SedlJa/Passman/_docs/app_archi.png

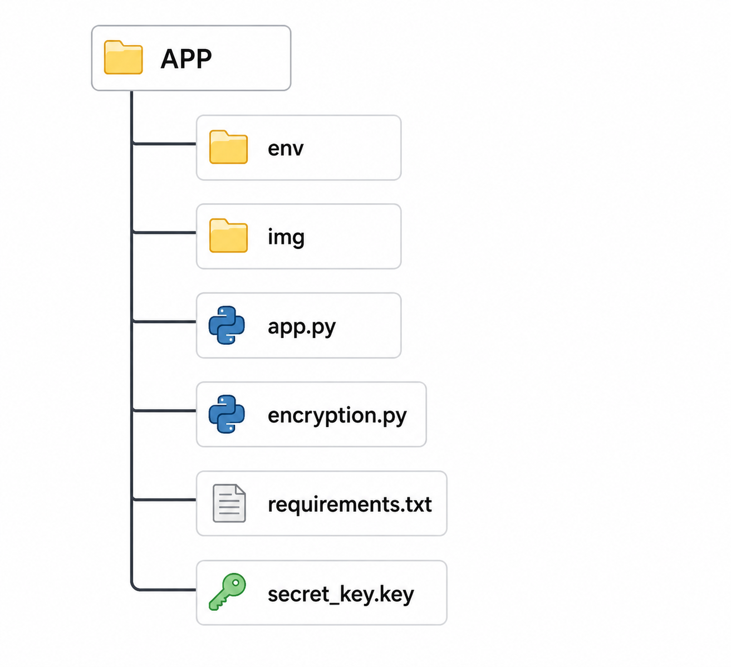
_docs/app_archi.png
