SedlJa/Passman/_docs/fw_diagram_bold.png

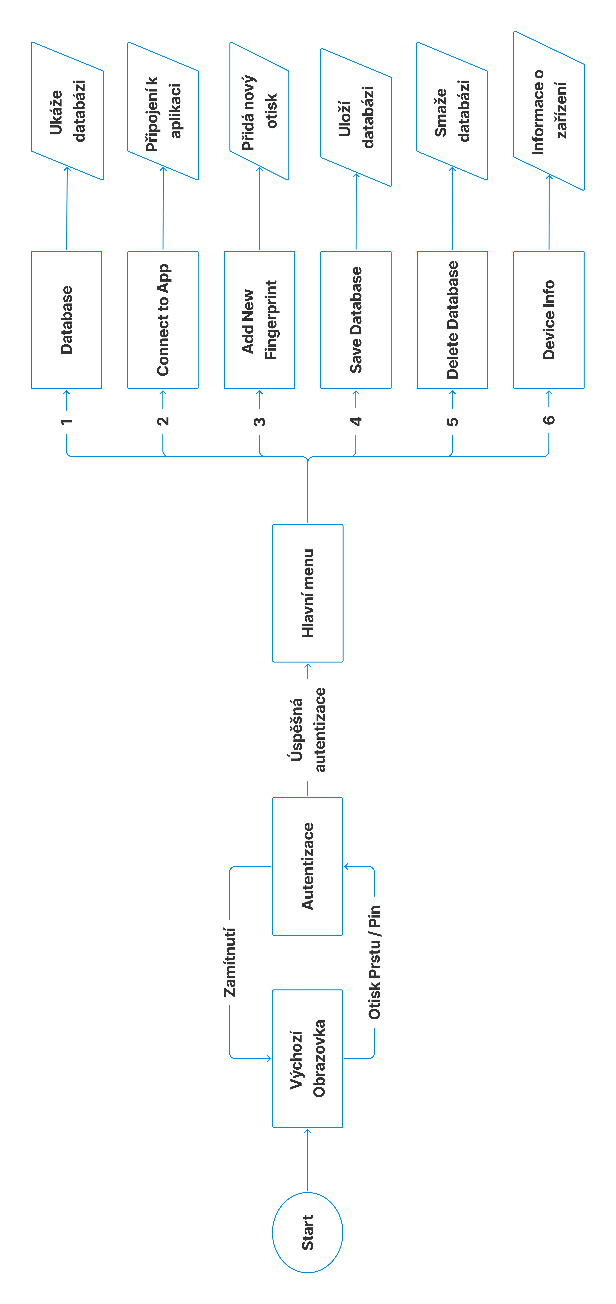
_docs/fw_diagram_bold.png
