SedlJa/Passman/_docs/layout_2v1.png

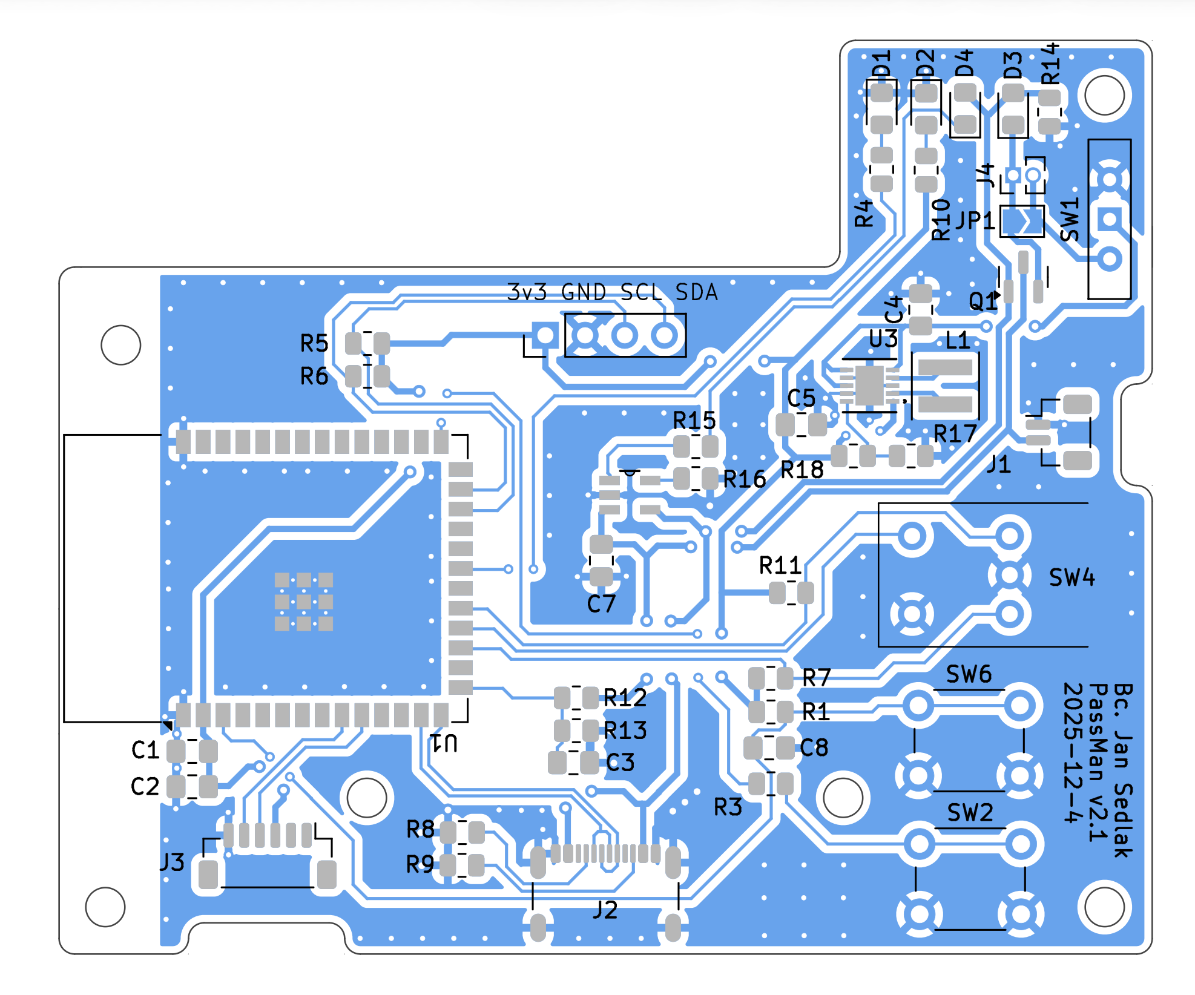
_docs/layout_2v1.png
