SedlJa/Passman/HW/Fusion/side2_view.png

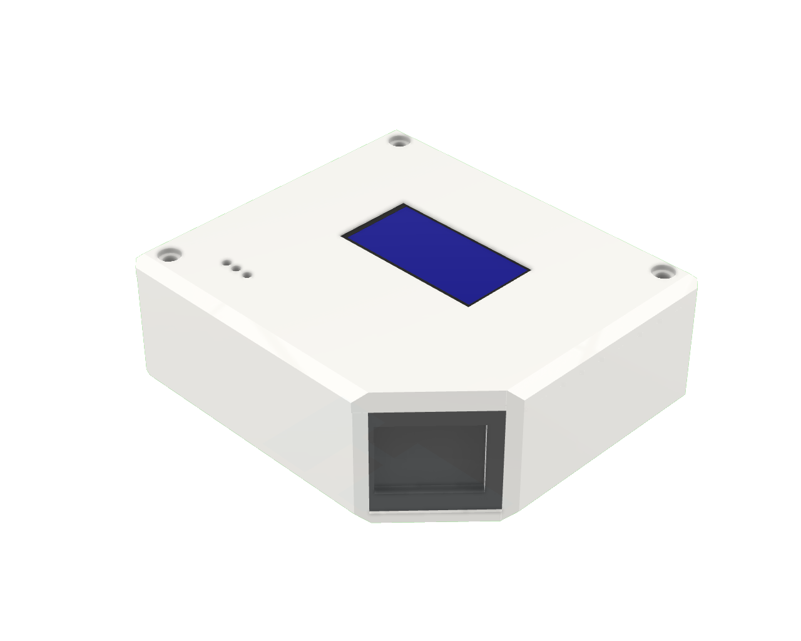
HW/Fusion/side2_view.png
