SedlJa/Passman/HW/Fusion/side_view2.png

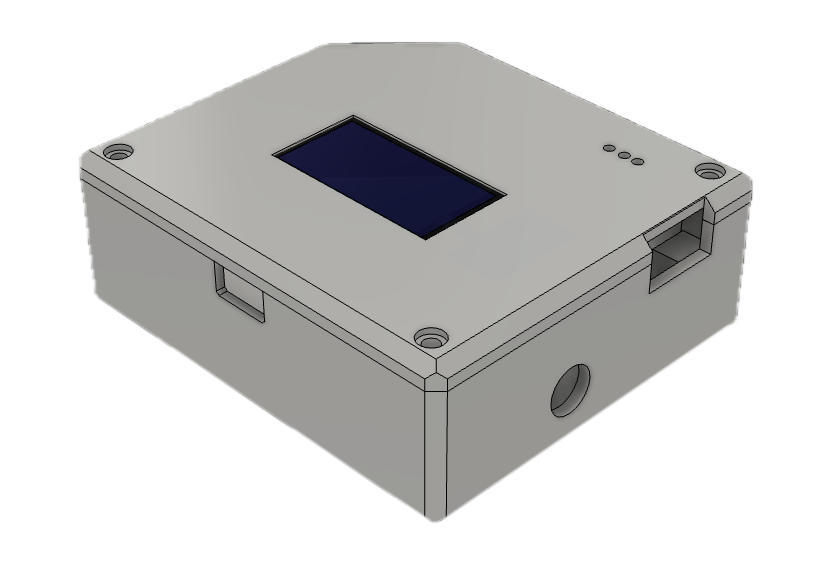
HW/Fusion/side_view2.png
