SedlJa/Passman/HW/Fusion/side_view.png

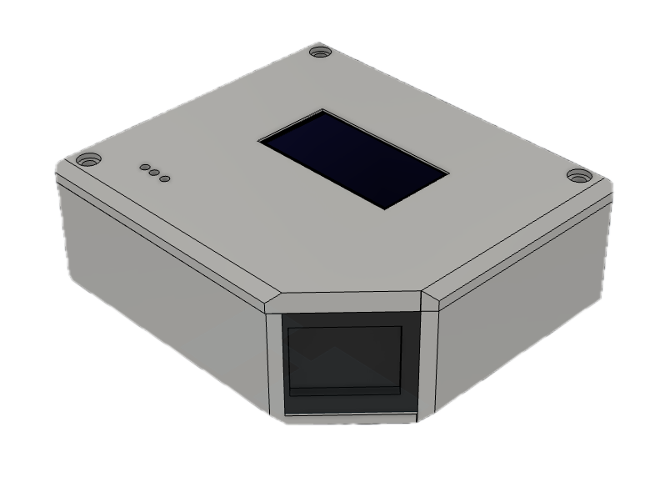
HW/Fusion/side_view.png
