SedlJa/Passman/HW/Fusion/sideview_device.png

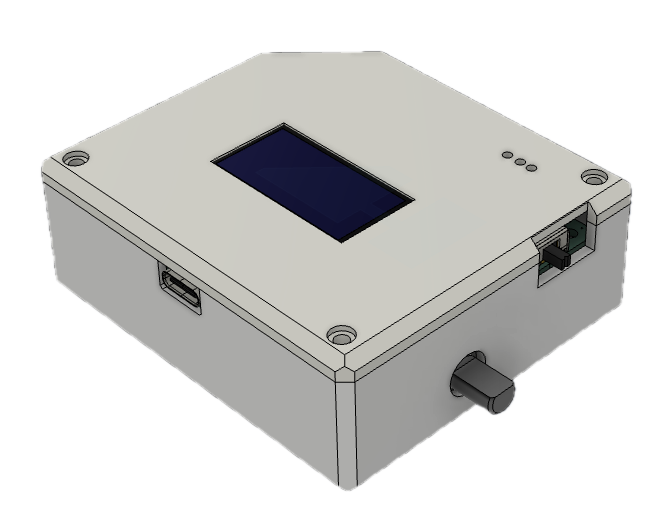
HW/Fusion/sideview_device.png
