SedlJa/Passman/HW/Fusion/top_view.png

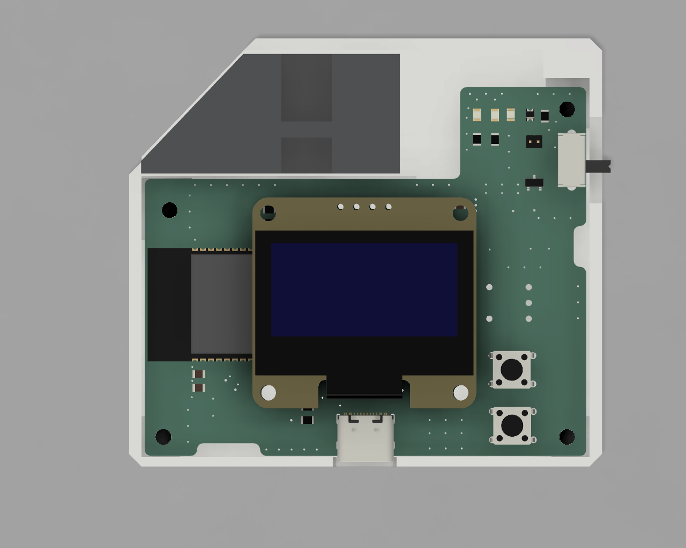
HW/Fusion/top_view.png
