SedlJa/Passman/HW/Fusion/top_view_box.png

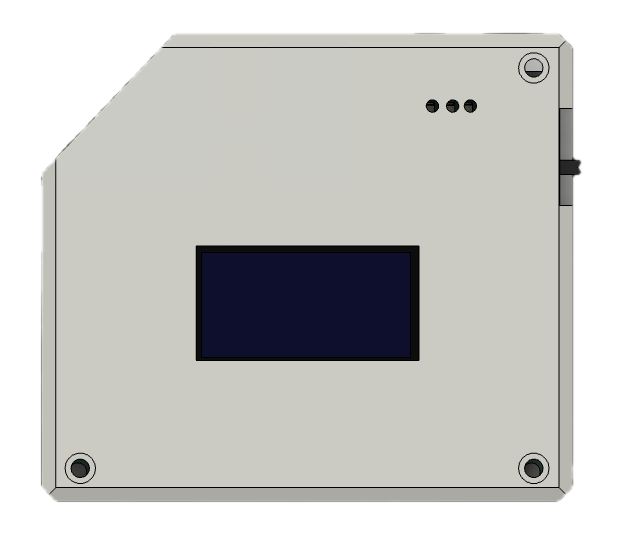
HW/Fusion/top_view_box.png
