SedlJa/Passman/HW/Fusion/top_view_device.png

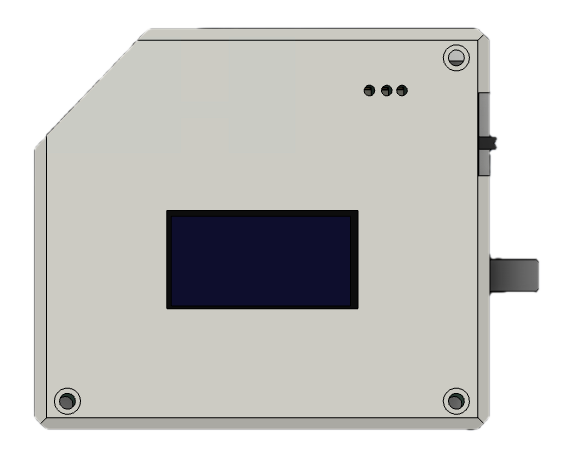
HW/Fusion/top_view_device.png
