SedlJa/Passman/HW/pcb_2v1.png

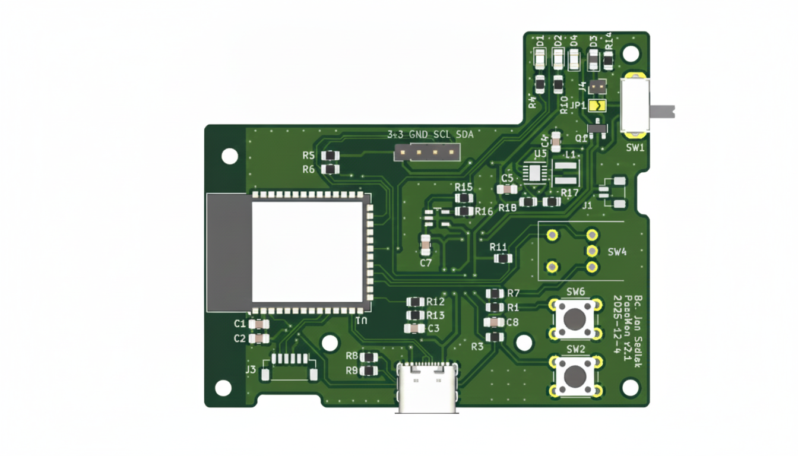
HW/pcb_2v1.png
