SedlJa/Passman/SW/firmware/src/oled.cpp

#include "oled.h"
#include "i2c_finder.h"
#include "database.h"

/* Defines */
#define DELAYTIME 1000
#define DISPLAYI2C_ADDR 0x3C
#define DISPLAYWIDTH 128
#define DISPLAYHEIGH 64
#define BATT_LVL 3 // battery level read pin

/* Create diplay instance */
Adafruit_SH1106G display = Adafruit_SH1106G(DISPLAYWIDTH, DISPLAYHEIGH, &Wire, -1);

/* Functions */

/* Battery lvl function */
int getBatteryLevelPercentage(int pin)
{
    int raw = analogRead(BATT_LVL);

    float v = (raw / 4095.0) * 3.3;

    // kompenzace děliče
    v *= 2.0;

    // Convert voltage to percentage
    float percentage = (v - 3.0) / (3.9 - 3.0) * 100.0; // Assuming 3.0V is 0% and 4.2V is 100%
    percentage = constrain(percentage, 0.0, 100.0);     // Clamp the value between 0% and 100%

    // Round percentage to the nearest multiple of 5
    percentage = round(percentage / 5.0) * 5.0;
    return percentage;
}

/**
 * @brief function that setups OLED display
 */
void display_setup()
{
    Wire.setPins(48, 47); // Set I2C pins [sda, scl ]
    Wire.begin();         // Inicializace I2C

    int state; // OLED I2C state
    state = find_I2C_addr();
    if (state == 0)
    {
        Serial.print("OLED display found.\r\n");
    }
    else if (state == 1)
    {
        Serial.println("No I2C device found.\r\n");
    }
    else if (state == 2)
    {
        Serial.println("Unknown error.\r\n");
    }

    display.begin(DISPLAYI2C_ADDR, true);
    display.clearDisplay();
    display.setTextColor(SH110X_WHITE);
    display.setTextSize(1);
}

void test_print(int rotaryVal)
{
    // put your main code here, to run repeatedly:
    display.setCursor(0, 7);
    display.println((String) "Teplota: 25C");
    display.println((String) "Tlak: 950hPa");
    display.println((String) "Vlhkost: 65%");
    display.println((String) "Loviskuju ZUZANKU");
    display.println((String) "Rotary value: " + (String)rotaryVal);
    display.display();
    delay(10);
    display.clearDisplay();
}

void getID(int rotaryVal)
{
    // put your main code here, to run repeatedly:
    display.setCursor(0, 20);
    display.println((String) "new ID: " + (String)rotaryVal);
    display.display();
    delay(10);
    display.clearDisplay();
}

/**
 * @brief function for displaying the fingerprint sensor while unlocking the device
 */
void unlockPage()
{
    // 1st stage
    display.clearDisplay();
    display.drawBitmap(0, 0, epd_bitmap_fpsensor, 128, 64, SH110X_WHITE);
    display.display();
    delay(20);
    display.clearDisplay();
}
/**
 * @brief Function that shows tick while authentication passed
 */
void unlockSuccessfull(int ledpin)
{
    // stage 1
    digitalWrite(ledpin, HIGH); // turn on LED
    display.clearDisplay();
    display.drawBitmap(0, 0, epd_bitmap_tick, 128, 64, SH110X_WHITE);
    display.display();
    delay(1000);
    display.clearDisplay();
    // stage 2
    display.drawBitmap(0, 0, epd_bitmap_tick2, 128, 64, SH110X_WHITE);
    display.display();
    delay(1000);
    display.clearDisplay();
    // stage 1
    display.drawBitmap(0, 0, epd_bitmap_tick3, 128, 64, SH110X_WHITE);
    display.display();
    delay(1000);
    display.clearDisplay();
    digitalWrite(ledpin, LOW); // Turn off led
}

/**
 * @brief function for displaying the first page
 */
void menuPage1()
{
    // put your main code here, to run repeatedly:
    display.clearDisplay();
    display.drawBitmap(0, 0, epd_bitmap_database, 128, 64, SH110X_WHITE);
    display.display();
    delay(10);
    display.clearDisplay();
}

/**
 * @brief function for displaying the second page
 */
void menuPage2()
{
    // put your main code here, to run repeatedly:
    display.clearDisplay();
    display.drawBitmap(0, 0, epd_bitmap_connect, 128, 64, SH110X_WHITE);
    display.display();
    delay(10);
    display.clearDisplay();
}

/* enroll FP */
void placeFP()
{
    display.clearDisplay();
    display.setCursor(30, 15);
    display.println("Place Finger");
    display.display();
    delay(10);
    display.clearDisplay();
}
void remove()
{
    display.clearDisplay();
    display.setCursor(30, 15);
    display.println("Remove Finger");
    display.display();
    delay(10);
    display.clearDisplay();
}
void addedFP()
{
    display.clearDisplay();
    display.setCursor(20, 15);
    display.println("Fingerprint added!");
    display.display();
    delay(10);
    display.clearDisplay();
}

void failFP()
{
    display.clearDisplay();
    display.setCursor(20, 15);
    display.println("No match found!");
    display.display();
    delay(10);
    display.clearDisplay();
}

/**
 * @brief function for displaying the fourth page
 */
void menuPage4()
{
    // put your main code here, to run repeatedly:
    display.clearDisplay();
    display.drawBitmap(0, 0, epd_bitmap_savedb, 128, 64, SH110X_WHITE);
    display.display();
    delay(10);
    display.clearDisplay();
}

/**
 * @brief function for displaying the fourth page
 */
void menuPage5()
{
    // put your main code here, to run repeatedly:
    display.clearDisplay();
    display.drawBitmap(0, 0, epd_bitmap_deleteall, 128, 64, SH110X_WHITE);
    display.display();
    delay(10);
    display.clearDisplay();
}

/**
 * @brief function for displaying the fourth page
 */
void menuPage6()
{
    // put your main code here, to run repeatedly:
    display.clearDisplay();
    display.drawBitmap(0, 0, epd_bitmap_devinfo, 128, 64, SH110X_WHITE);
    display.display();
    delay(10);
    display.clearDisplay();
}

void menuPage3()
{
    display.clearDisplay();
    display.drawBitmap(0, 0, epd_bitmap_addFP, 128, 64, SH110X_WHITE);
    display.display();
    delay(10);
    display.clearDisplay();
}

/**
 * @brief Function for choose upload/download page
 */
void uploadPage()
{
    display.clearDisplay();
    display.drawBitmap(0, 0, epd_bitmap_upload, 128, 64, SH110X_WHITE);
    display.display();
    delay(10);
    display.clearDisplay();
}
/**
 * @brief Function for choose upload/download page
 */
void downloadPage()
{
    display.clearDisplay();
    display.drawBitmap(0, 0, epd_bitmap_download, 128, 64, SH110X_WHITE);
    display.display();
    delay(10);
    display.clearDisplay();
}

/**
 * @brief Page that shows each database item
 */
void databasePage(int dbEntry)
{
    display.setCursor(0, 0);
    display.println((String)db.id[dbEntry]);
    display.println((String) "");
    display.println((String) "Username:");
    display.println((String)db.username[dbEntry]);
    display.println((String) " ");
    display.println((String) " ");
    display.println((String) "Password");
    display.println((String)db.password[dbEntry]);
    display.display();
    delay(10);
    display.clearDisplay();
}

/**
 * @brief function for displaying the author info Page
 */
void deviceInfo()
{
    // Open the JSON file
    FILE *file = fopen("/spiffs/device.json", "r");
    if (!file)
    {
        Serial.println("Failed to open deviceinfo.json");
        return;
    }

    // Read the file into a buffer
    char buffer[256];
    size_t bytesRead = fread(buffer, 1, sizeof(buffer) - 1, file);
    buffer[bytesRead] = '\0'; // Null-terminate the buffer
    fclose(file);

    // Parse the JSON data
    StaticJsonDocument<512> doc;
    DeserializationError error = deserializeJson(doc, buffer);
    if (error)
    {
        Serial.print("Failed to parse JSON: ");
        Serial.println(error.c_str());
        return;
    }

    // Extract data from JSON
    JsonObject deviceInfo = doc["deviceInfo"];
    const char *deviceName = deviceInfo["device Name"];
    const char *fwVersion = deviceInfo["FW Version"];
    const char *hwVersion = deviceInfo["HW Version"];
    const char *serialNumber = deviceInfo["SN"];

    // Display the data on the OLED
    display.clearDisplay();
    display.setCursor(0, 0);
    display.println("Device Info:");
    display.println((String) "");
    display.println((String) "Project: " + deviceName);
    display.println((String) "FW Ver:  " + fwVersion);
    display.println((String) "HW Ver:  " + hwVersion);
    display.println((String) "SN:      " + serialNumber);
    display.println((String) "Battery: " + getBatteryLevelPercentage(BATT_LVL) + " %");
    display.display();
}
// 'database', 128x64px
const unsigned char epd_bitmap_database[] PROGMEM = {
    0x00, 0x00, 0x00, 0x00, 0x00, 0x00, 0x00, 0x00, 0x00, 0x00, 0x00, 0x00, 0x00, 0x00, 0x00, 0x00,
    0x00, 0x00, 0x00, 0x00, 0x00, 0x00, 0x00, 0x00, 0x00, 0x00, 0x00, 0x00, 0x00, 0x00, 0x00, 0x00,
    0x00, 0x00, 0x00, 0x00, 0x00, 0x00, 0x00, 0x00, 0x00, 0x00, 0x00, 0x00, 0x00, 0x00, 0x00, 0x00,
    0x00, 0x00, 0x00, 0x00, 0x00, 0x00, 0x00, 0x00, 0x00, 0x00, 0x00, 0x00, 0x00, 0x00, 0x00, 0x00,
    0x00, 0x00, 0x00, 0x00, 0x00, 0x00, 0x00, 0x00, 0x00, 0x00, 0x00, 0x00, 0x00, 0x00, 0x00, 0x00,
    0x00, 0x00, 0x00, 0x00, 0x00, 0x00, 0x00, 0x00, 0x00, 0x00, 0x00, 0x00, 0x00, 0x00, 0x00, 0x00,
    0x00, 0x00, 0x00, 0x00, 0x00, 0x00, 0x00, 0x00, 0x00, 0x00, 0x00, 0x00, 0x00, 0x00, 0x00, 0x00,
    0x00, 0x00, 0x00, 0x00, 0x00, 0x00, 0x00, 0x00, 0x00, 0x00, 0x00, 0x00, 0x00, 0x00, 0x00, 0x00,
    0x00, 0x00, 0x00, 0x00, 0x00, 0x00, 0x00, 0x00, 0x00, 0x00, 0x00, 0x00, 0x00, 0x00, 0x00, 0x00,
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
    epd_bitmap_database,
    epd_bitmap_savedb,
    epd_bitmap_download,
    epd_bitmap_upload,
    epd_bitmap_devinfo,
    epd_bitmap_deleteall,
    epd_bitmap_fpsensor,
    epd_bitmap_tick,
    epd_bitmap_tick2,
    epd_bitmap_tick3,
    epd_bitmap_connect,
    epd_bitmap_addFP,
};
