SedlJa/Passman/SW/firmware/src/encryption.cpp

/* Includes */
#include "encryption.h"
#include "esp_efuse.h"

/* Defines */
static uint8_t secret_key[AES_KEY_SIZE];
static bool secret_key_loaded = false;

/* Functions */
static bool load_secret_key_from_efuse()
{
    if (secret_key_loaded)
    {
        return true;
    }

    esp_err_t err = esp_efuse_read_block(EFUSE_BLK_USER_DATA, secret_key, 0, AES_KEY_SIZE * 8);
    if (err != ESP_OK)
    {
        Serial.printf("Error: Failed to read AES key from eFuse. Code: %d\n", err);
        return false;
    }

    bool key_is_empty = true;
    for (size_t i = 0; i < AES_KEY_SIZE; i++)
    {
        if (secret_key[i] != 0)
        {
            key_is_empty = false;
            break;
        }
    }

    if (key_is_empty)
    {
        Serial.println("Error: AES key in eFuse is empty.");
        return false;
    }

    secret_key_loaded = true;
    return true;
}

void print_secret_key_debug()
{
    if (!load_secret_key_from_efuse())
    {
        Serial.println("eFuse AES key debug: unavailable");
        return;
    }

    Serial.print("eFuse AES key HEX: ");
    for (size_t i = 0; i < AES_KEY_SIZE; i++)
    {
        if (secret_key[i] < 0x10)
        {
            Serial.print("0");
        }
        Serial.print(secret_key[i], HEX);
        if (i < AES_KEY_SIZE - 1)
        {
            Serial.print(" ");
        }
    }
    Serial.println();

    Serial.print("eFuse AES key ASCII: ");
    Serial.write(secret_key, AES_KEY_SIZE);
    Serial.println();
}

/**
 * @brief encrypt data using AES
 *
 * @param plaintext plain text to be encrypted
 * @retval base64_buf data
 */
String encrypt_data(const char *plaintext)
{
    if (!load_secret_key_from_efuse())
    {
        return {};
    }

    mbedtls_aes_context aes_ctx;
    size_t plaintext_len = strlen(plaintext);

    // 1. Generate a new, random IV (16 bytes)
    uint8_t iv[16];
    // Using a simple method for example. For production, use a secure RNG like esp_fill_random()
    for (int i = 0; i < 16; i++)
    {
        iv[i] = random();
    }

    // 2. Pad the plaintext (PKCS7/PKCS5 padding)
    size_t padded_len = plaintext_len + (16 - (plaintext_len % 16));
    std::vector<uint8_t> padded_plaintext(padded_len);
    memcpy(padded_plaintext.data(), plaintext, plaintext_len);

    // Apply PKCS7 padding (mbedTLS does not have a built-in pad/unpad function for this mode)
    uint8_t padding_value = padded_len - plaintext_len;
    for (size_t i = plaintext_len; i < padded_len; i++)
    {
        padded_plaintext[i] = padding_value;
    }

    // 3. Initialize the AES context
    mbedtls_aes_init(&aes_ctx);
    if (mbedtls_aes_setkey_enc(&aes_ctx, secret_key, KEY_BITS) != 0)
    {
        Serial.println("Error: Failed to set encryption key.");
        mbedtls_aes_free(&aes_ctx);
        return {};
    }

    // 4. Encrypt
    std::vector<uint8_t> ciphertext(padded_len);
    uint8_t iv_copy[16];
    memcpy(iv_copy, iv, 16); // IV must be copied for mbedtls_aes_crypt_cbc

    if (mbedtls_aes_crypt_cbc(&aes_ctx, MBEDTLS_AES_ENCRYPT, padded_len, iv_copy, padded_plaintext.data(), ciphertext.data()) != 0)
    {
        mbedtls_aes_free(&aes_ctx);
        return {};
    }

    mbedtls_aes_free(&aes_ctx);

    // 5. Combine IV and Ciphertext for transmission
    std::vector<uint8_t> final_payload;
    final_payload.insert(final_payload.end(), iv, iv + 16);                          // Add IV
    final_payload.insert(final_payload.end(), ciphertext.begin(), ciphertext.end()); // Add Ciphertext

    if (!final_payload.empty())
    {
        // Convert the final IV + Ciphertext payload to Base64
        size_t output_len;
        mbedtls_base64_encode(NULL, 0, &output_len, final_payload.data(), final_payload.size());
        std::vector<unsigned char> base64_buf(output_len);
        mbedtls_base64_encode(base64_buf.data(), base64_buf.size(), &output_len, final_payload.data(), final_payload.size());

        return String((char *)base64_buf.data());
    }
    else
    {
        Serial.println("Encryption failed!");
        return String();
    }
}

/**
 * @brief Decypt data from serial port in base64 encoding
 *
 * @param base64_encrypted_data input String in base64 encodin
 * @return Decrypted String, unpadded plaintext, Empty if failure
 */
String decrypt_data(const String &base64_encrypted_data)
{
    if (!load_secret_key_from_efuse())
    {
        return "";
    }

    // 1. Base64 Decode the input String
    size_t decoded_len = 0;
    const unsigned char *input_ptr = (const unsigned char *)base64_encrypted_data.c_str();
    size_t input_len = base64_encrypted_data.length();

    // Allocate buffer for Base64 decoding
    int ret = mbedtls_base64_decode(nullptr, 0, &decoded_len, input_ptr, input_len);

    if (ret != 0 && ret != MBEDTLS_ERR_BASE64_BUFFER_TOO_SMALL)
    {
        Serial.printf("Error: Base64 decoding pre-check failed. Code: %d\n", ret);
        return "";
    }

    std::vector<uint8_t> decoded_payload(decoded_len);

    // Perform the actual decoding
    ret = mbedtls_base64_decode(decoded_payload.data(), decoded_len, &decoded_len, input_ptr, input_len);

    if (ret != 0)
    {
        Serial.printf("Error: Base64 decoding failed. Code: %d\n", ret);
        return "";
    }

    if (decoded_len < AES_BLOCK_SIZE)
    {
        Serial.println("Error: Decoded payload is too small for IV.");
        return "";
    }

    // 2. Split the IV and Ciphertext
    std::vector<uint8_t> iv(decoded_payload.begin(), decoded_payload.begin() + AES_BLOCK_SIZE);
    std::vector<uint8_t> ciphertext(decoded_payload.begin() + AES_BLOCK_SIZE, decoded_payload.end());
    size_t ciphertext_len = ciphertext.size();

    if (ciphertext_len == 0 || ciphertext_len % AES_BLOCK_SIZE != 0)
    {
        Serial.println("Error: Ciphertext length invalid or not block aligned.");
        return "";
    }

    // 3. Decrypt the data (AES-128-CBC)
    std::vector<uint8_t> decrypted_padded(ciphertext_len);
    mbedtls_aes_context aes_ctx;
    mbedtls_aes_init(&aes_ctx);

    if (mbedtls_aes_setkey_dec(&aes_ctx, secret_key, KEY_BITS) != 0)
    {
        Serial.println("Error: Failed to set decryption key.");
        mbedtls_aes_free(&aes_ctx);
        return "";
    }

    uint8_t iv_copy[AES_BLOCK_SIZE];
    std::copy(iv.begin(), iv.end(), iv_copy);

    ret = mbedtls_aes_crypt_cbc(&aes_ctx, MBEDTLS_AES_DECRYPT, ciphertext_len, iv_copy, ciphertext.data(), decrypted_padded.data());
    mbedtls_aes_free(&aes_ctx);

    if (ret != 0)
    {
        Serial.printf("Error: AES CBC decryption failed. Code: %d\n", ret);
        return "";
    }

    // 4. Remove PKCS7 Padding
    uint8_t padding_value = decrypted_padded.back();

    if (padding_value == 0 || padding_value > AES_BLOCK_SIZE || padding_value > decrypted_padded.size())
    {
        Serial.println("Warning: Invalid padding value. Returning raw data.");
        // If padding is invalid, we return the raw decrypted data (or an error)
        return String((char *)decrypted_padded.data(), decrypted_padded.size());
    }

    size_t unpadded_len = decrypted_padded.size() - padding_value;

    // Extract the final unpadded plaintext and return as Arduino String
    return String((char *)decrypted_padded.data(), unpadded_len);
}
