SedlJa/Passman/SW/firmware/include/fpcheck.h

/*
    Header file for fingerprint sensor check
*/

#ifndef FPCHECK_H

#define FPCHECK_H

/* Includes */
#include <Adafruit_Fingerprint.h>
#include "Arduino.h"
#include "oled.h"

/* Functions declarations */
uint8_t getFingerprintID(); // Function which handles fingerprint input

int getFingerprintIDez(); // Function to get fingerprint ID from database

void fpSetup();                              // Function to init fpSerial and check if sensor is found
uint8_t getFingerprintEnroll(int id);        // function to add fingerprint
int fpUnlockDevice(int handler, int ledpin); // Function that runs authentification procedure

#endif
