SedlJa/Passman/SW/firmware/include/authentication.h

/*
    Header file for Authentication
*/

#ifndef AUTHENTICATION_H

#define AUTHENTICATION_H

/* Includes */
#include <Arduino.h>
#include "rotary.h"
#include "fpcheck.h"
#include "oled.h"

/* PIN page */
int comparePins(int setPin[], int insertedPin[]);
void insertPin(int fail);
void unlockProcedure();

#endif // AUTHENTICATION_H
